sebastian-lenz/rfid-hub/src/ui/Sprites.h

#ifndef RFID_SPRITES
#define RFID_SPRITES

namespace sprites {
  static unsigned char power[] = {
    0x00, 0x00, 0x20, 0x00, 0xAC, 0x01, 0x24, 0x01, 0x22, 0x02, 0x22, 0x02,
    0x02, 0x02, 0x04, 0x01, 0x8C, 0x01, 0x70, 0x00, 0x00, 0x00,
  };

  static unsigned char settings[] = {
    0xC0, 0x00, 0xF0, 0x03, 0xE0, 0x03, 0x18, 0x07, 0x7E, 0x07, 0x7E, 0x03,
    0xE7, 0x02, 0xE7, 0x00, 0x7E, 0x00, 0x7E, 0x00, 0x18, 0x00,
  };

  static unsigned char edit[] = {
    0x00, 0x00, 0x00, 0x06, 0x00, 0x05, 0x80, 0x02, 0xC0, 0x01, 0xE0, 0x00,
    0x70, 0x00, 0x30, 0x00, 0x0B, 0x00, 0x00, 0x00, 0x00, 0x00,
  };

  static unsigned char radioOff[] = {
    0x00, 0x00, 0x70, 0x00, 0x8C, 0x01, 0x04, 0x01, 0x02, 0x02, 0x02, 0x02,
    0x02, 0x02, 0x04, 0x01, 0x8C, 0x01, 0x70, 0x00, 0x00, 0x00,
  };

  static unsigned char radioOn[] = {
    0x00, 0x00, 0x70, 0x00, 0x8C, 0x01, 0x74, 0x01, 0xFA, 0x02, 0xFA, 0x02,
    0xFA, 0x02, 0x74, 0x01, 0x8C, 0x01, 0x70, 0x00, 0x00, 0x00,
  };

  static unsigned char trash[] = {
    0x00, 0x00, 0x20, 0x00, 0x50, 0x00, 0xFE, 0x03, 0x00, 0x00, 0xFC, 0x01,
    0x54, 0x01, 0x54, 0x01, 0x54, 0x01, 0x54, 0x01, 0xFC, 0x01,
  };

  static unsigned char more[] = {
    0x7F, 0x00, 0x41, 0x00, 0x41, 0x01, 0x41, 0x01, 0x41, 0x05, 0x7F, 0x05,
    0x00, 0x05, 0xFC, 0x05, 0x00, 0x04, 0xF0, 0x07, 0x00, 0x00,
  };

  static unsigned char info[] = {
    0x00, 0x00, 0x70, 0x00, 0x8C, 0x01, 0x24, 0x01, 0x02, 0x02, 0x22, 0x02,
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
      0x01, 0x04, 0x01, 0x04, 0x02, 0x02, 0x04, 0x01, 0xF8, 0x00,
    },
    {
      0xF8, 0x00, 0x0C, 0x01, 0x1E, 0x02, 0x19, 0x04, 0x31, 0x04, 0x21, 0x04,
      0x01, 0x04, 0x01, 0x04, 0x02, 0x02, 0x04, 0x01, 0xF8, 0x00,
    }
  };
}

#endif
